mlaiacker/max-lader/software/avr/pwm.h

/* 
* max-Lader 
* entwickelt von:
* Maximilian Laiacker post@mlaiacker.de http://mlaiacker.de/
*/


#ifndef PWM_H
#define PWM_H
#include "hardware.h"

//void pwmInit(void);
void pwmSet(signed short value);

#endif
